nagius/ESPower/Docs/A Lithium Battery Charger with Load Sharing | Zak’s Electronics Blog ~*_files/a_data/Layout5default.webp

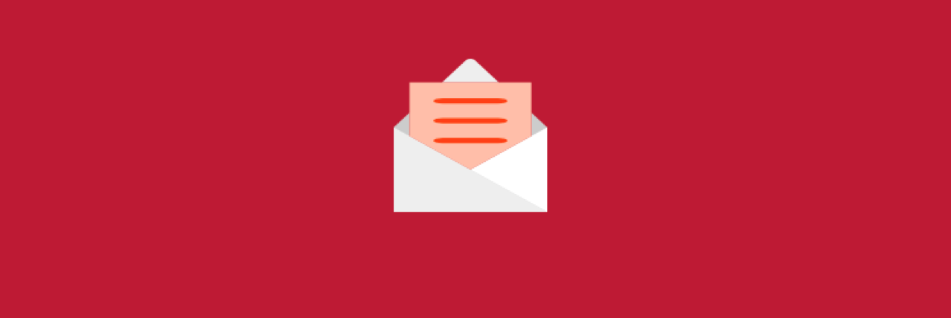
Docs/A Lithium Battery Charger with Load Sharing | Zak’s Electronics Blog ~*_files/a_data/Layout5default.webp
