nagius/ESPower/Docs/The TP4056 Lithium Ion_polymer Battery Charger IC_2_files/charger-powerpath-pmosfet-off.webp

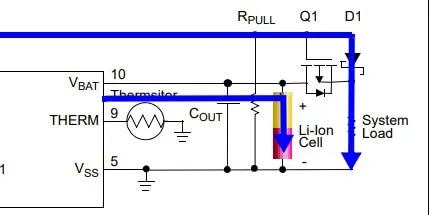
Docs/The TP4056 Lithium Ion_polymer Battery Charger IC_2_files/charger-powerpath-pmosfet-off.webp
