nagius/ESPower/Docs/The TP4056 Lithium Ion_polymer Battery Charger IC_2_files/joystick-capped-400r.webp

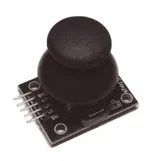
Docs/The TP4056 Lithium Ion_polymer Battery Charger IC_2_files/joystick-capped-400r.webp
