nagius/ESPower/Docs/The TP4056 Lithium Ion_polymer Battery Charger IC_2_files/mcp41010-block-diagram-enh.webp

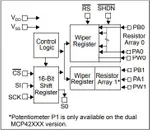
Docs/The TP4056 Lithium Ion_polymer Battery Charger IC_2_files/mcp41010-block-diagram-enh.webp
