nagius/ESPower/Docs/The TP4056 Lithium Ion_polymer Battery Charger IC_2_files/tp4056-breakout-boad-schematic-enh.webp

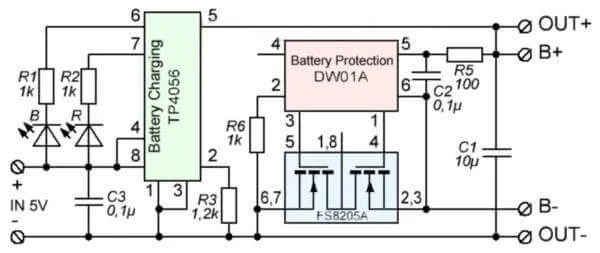
Docs/The TP4056 Lithium Ion_polymer Battery Charger IC_2_files/tp4056-breakout-boad-schematic-enh.webp
