nagius/ESPower/Photos/ESpower-v1.jpg

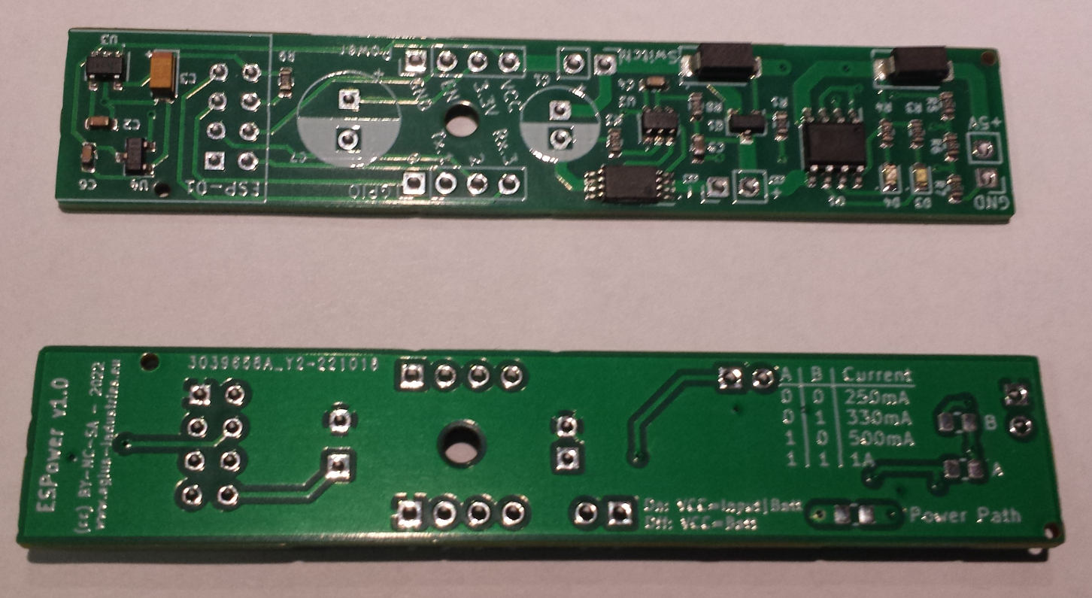
Photos/ESpower-v1.jpg
